zhyma/vr15/3d_model/stl/tools/drilling_position.STL

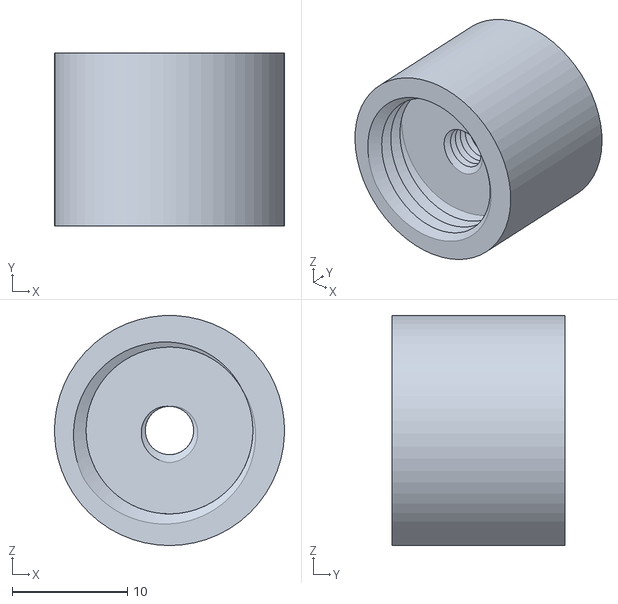
[picture p89: CAD file, 2021-12-30]
3d_model/stl/tools/drilling_position.STL
20.0 x 15.0 x 20.0
