zhyma/vr15/3d_model/stl/accessory/charging_handle_block.STL

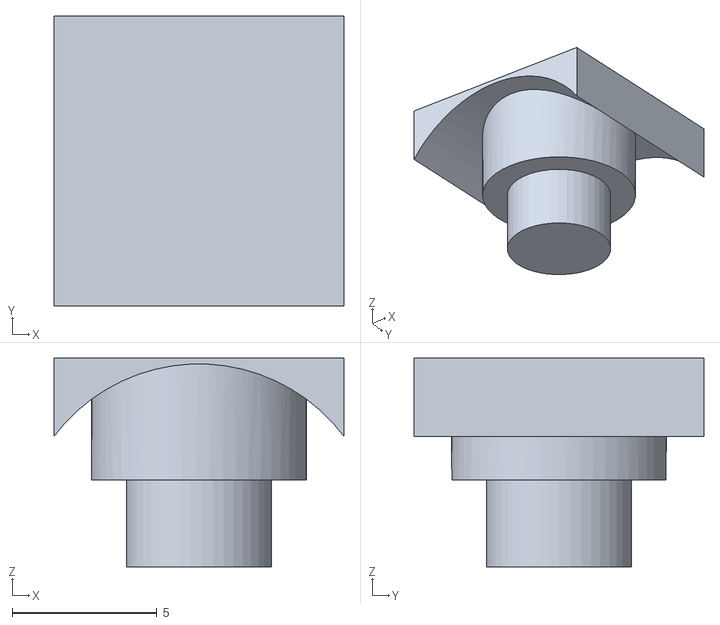
[picture p90: CAD file, 2021-12-30]
3d_model/stl/accessory/charging_handle_block.STL
10.0 x 10.0 x 7.20
