zhyma/vr15/3d_model/step/vr15_upper_r.STEP

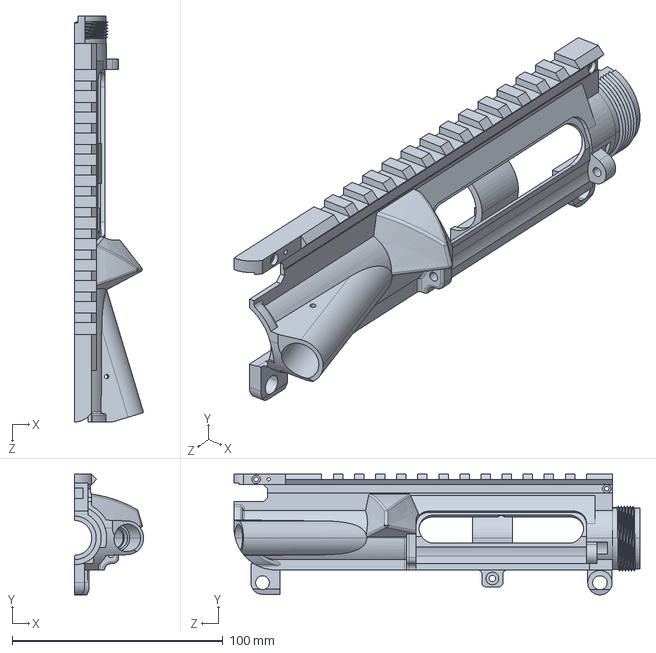
[picture p91: CAD file, 2021-12-30]
3d_model/step/vr15_upper_r.STEP
32.8 x 57.3 x 192.5 mm
