zhyma/vr15/3d_model/stl/accessory/tof_spacer.STL

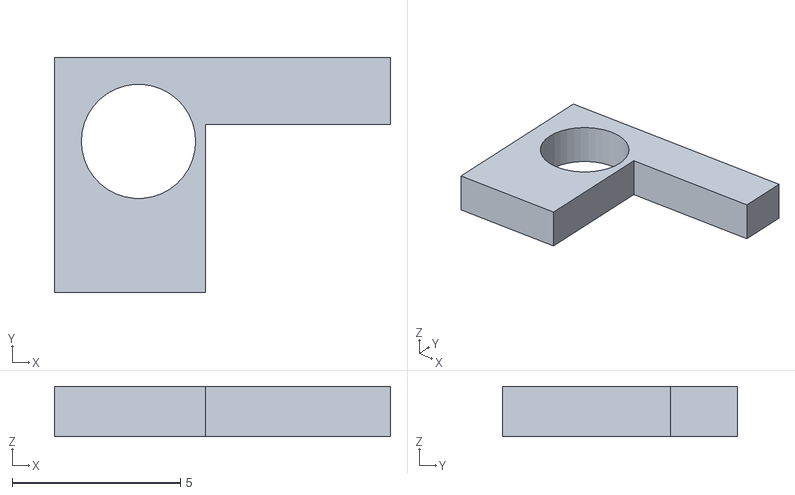
[picture p92: CAD file, 2021-12-30]
3d_model/stl/accessory/tof_spacer.STL
10.0 x 7.00 x 1.50
