zhyma/vr15/3d_model/stl/accessory/buffer_spacer.STL

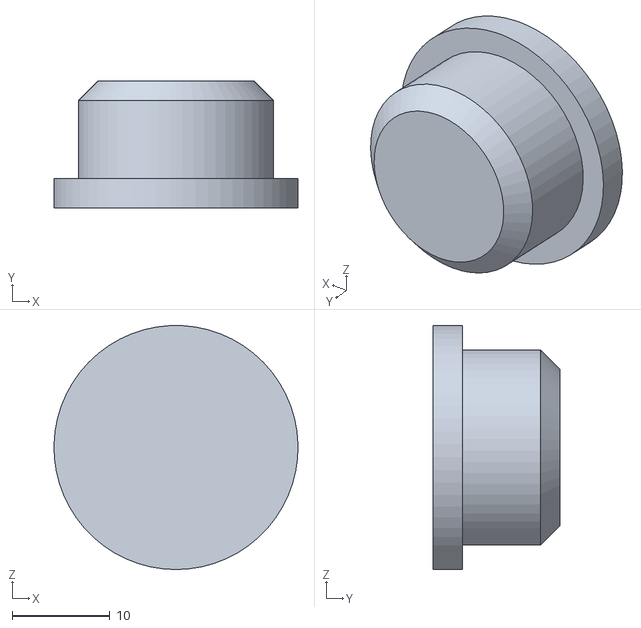
[picture p93: CAD file, 2021-12-30]
3d_model/stl/accessory/buffer_spacer.STL
25.0 x 13.0 x 25.0
