zhyma/vr15/3d_model/step/selector.STEP

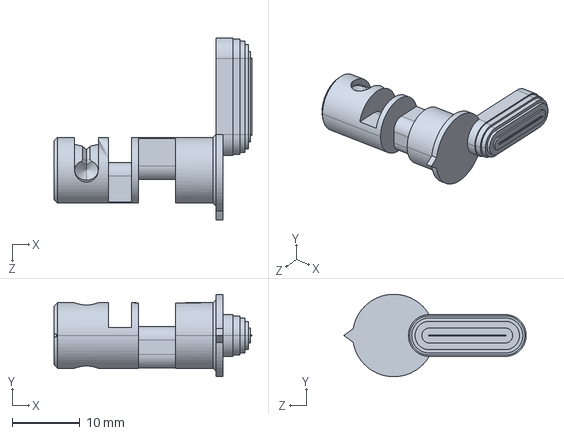
[picture p94: CAD file, 2021-12-30]
3d_model/step/selector.STEP
29.3 x 12.2 x 27.0 mm
