zhyma/vr15/3d_model/step/vr15_lower.STEP

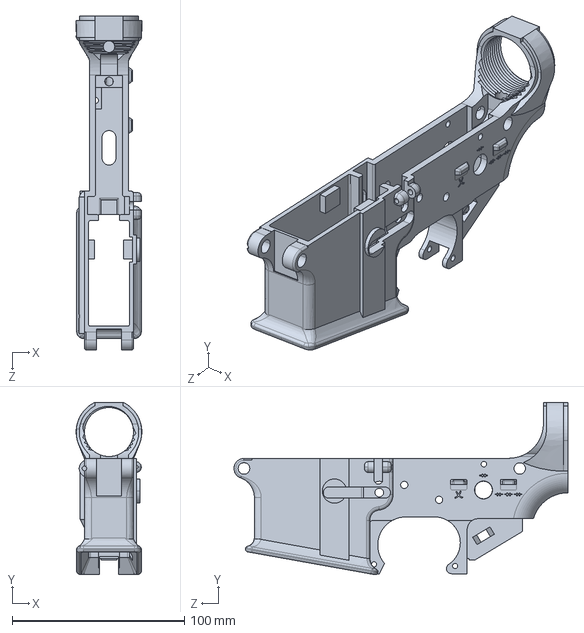
[picture p95: CAD file, 2021-12-30]
3d_model/step/vr15_lower.STEP
38.1 x 100.1 x 193.8 mm
