zhyma/vr15/3d_model/step/vr15_upper_l.STEP

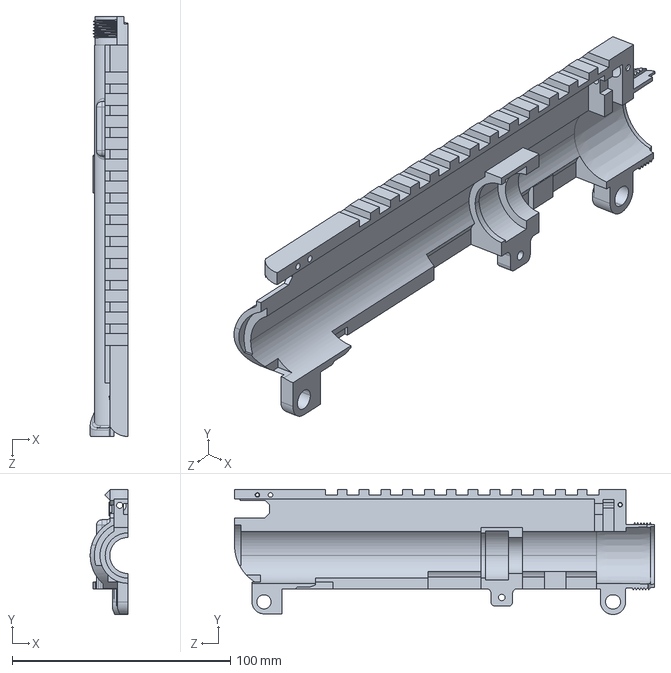
[picture p96: CAD file, 2021-12-30]
3d_model/step/vr15_upper_l.STEP
17.2 x 57.3 x 192.5 mm
